et7ad/esp_athan/hardware/pcb/athan_kicad/production_files_screenshots/2.jpg

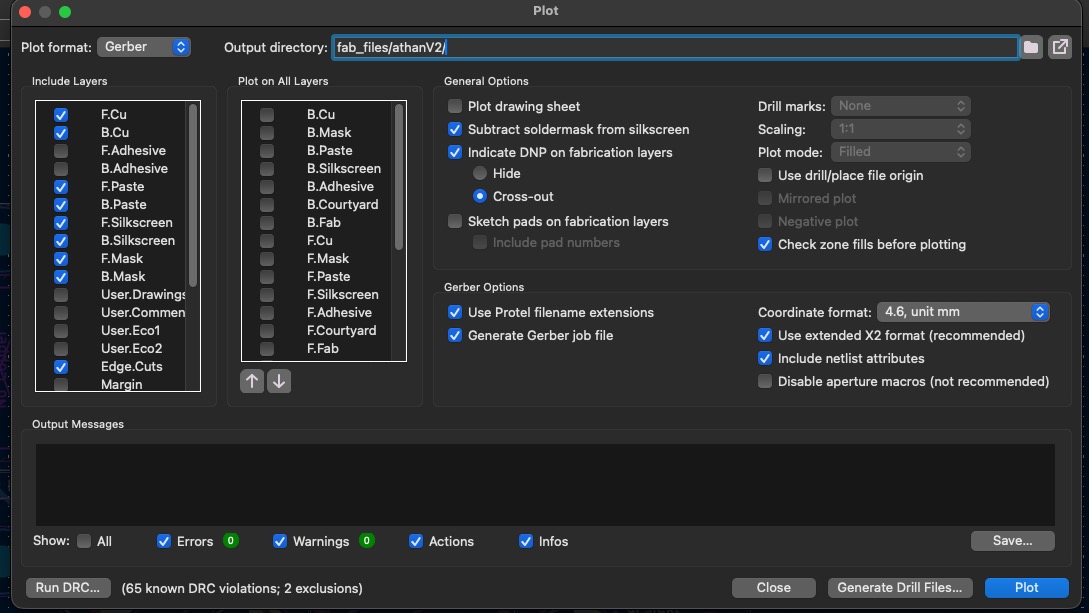
hardware/pcb/athan_kicad/production_files_screenshots/2.jpg
