et7ad/esp_athan/hardware/pcb/athan_kicad/production_files_screenshots/3.jpg

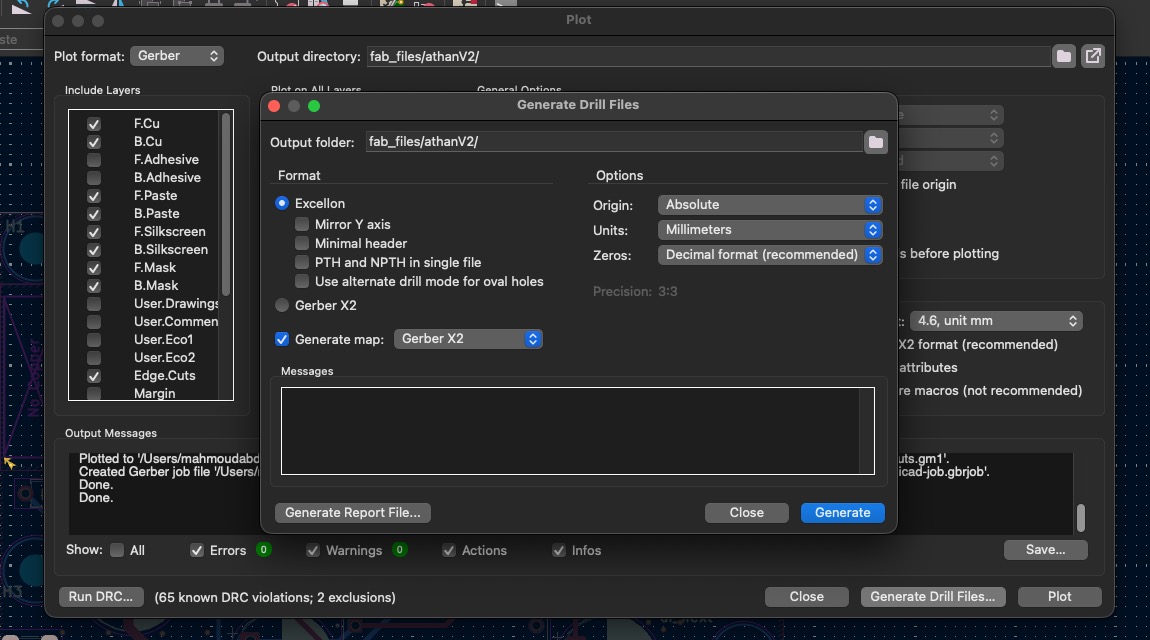
hardware/pcb/athan_kicad/production_files_screenshots/3.jpg
