et7ad/esp_athan/scripts/parse_Islamicfinder/parse_islamicfinder_yearly_get_html.jpg

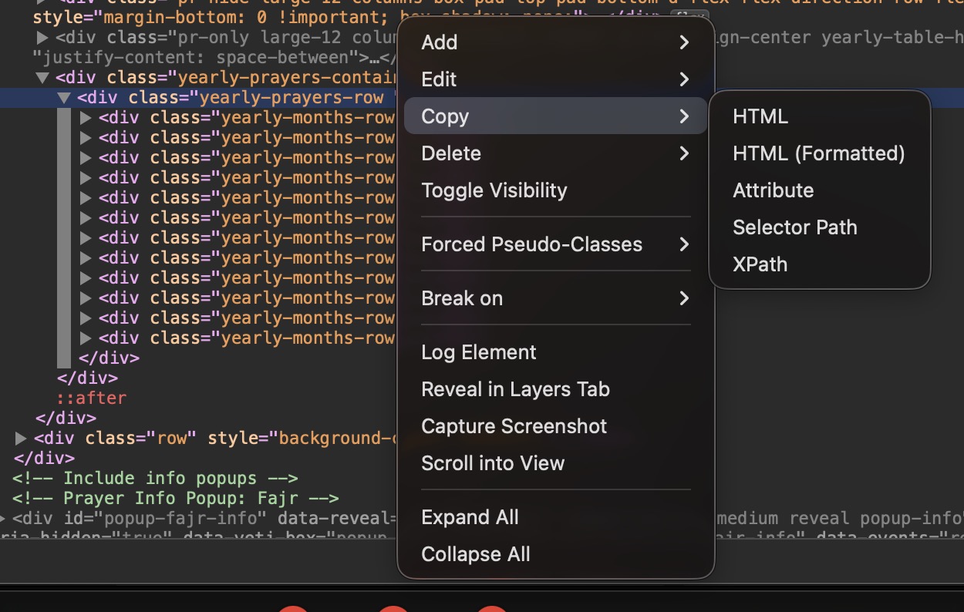
scripts/parse_Islamicfinder/parse_islamicfinder_yearly_get_html.jpg
